snakeye/matrix-clock/src/MatrixClock/clock/marquee.h

/*
 * marquee.h
 *
 * Created: 01.02.2014 15:29:24
 *  Author: snakeye
 */ 


#ifndef MARQUEE_H_
#define MARQUEE_H_


void start_marquee(const char* str, uint8_t times);
void animate_marquee();


#endif /* MARQUEE_H_ */
